wintermutepi/hexasense/doc/IMG_2468_.jpg

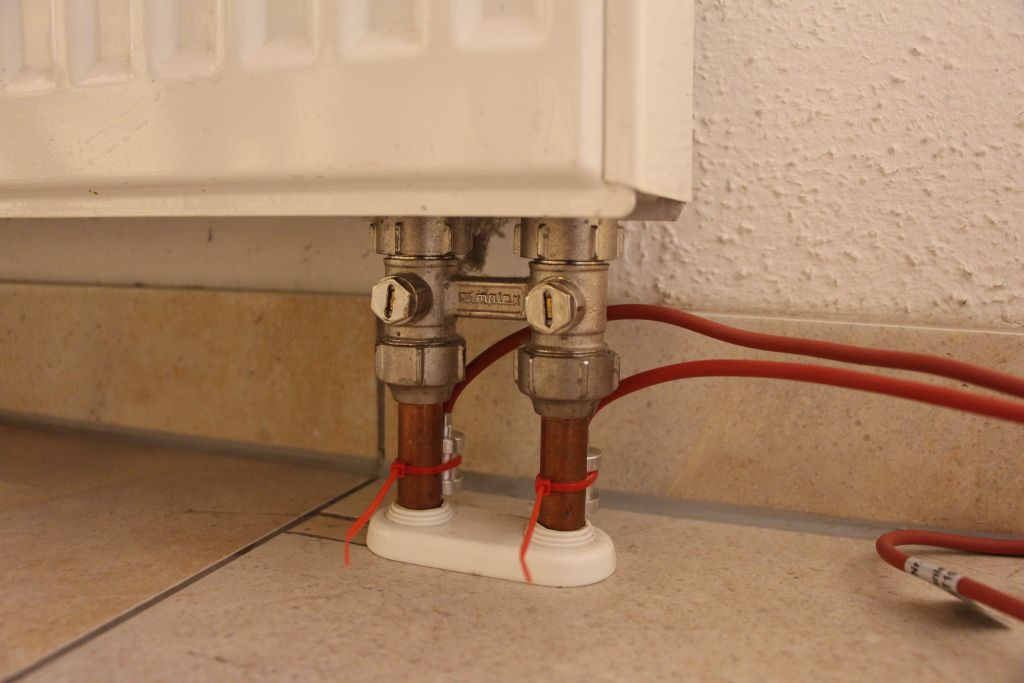
doc/IMG_2468_.jpg
