wintermutepi/hexasense/firmware/button.h

#ifndef BUTTON_H
#define BUTTON_H 1

#include <stdlib.h>
#include <stdbool.h>


void button_init(void);
bool is_button0_pressed(void);
bool is_button1_pressed(void);
bool is_button2_pressed(void);

#endif /* BUTTON_H */
